GabiBrawl/Nibunkatsu/assets/day2image5.png

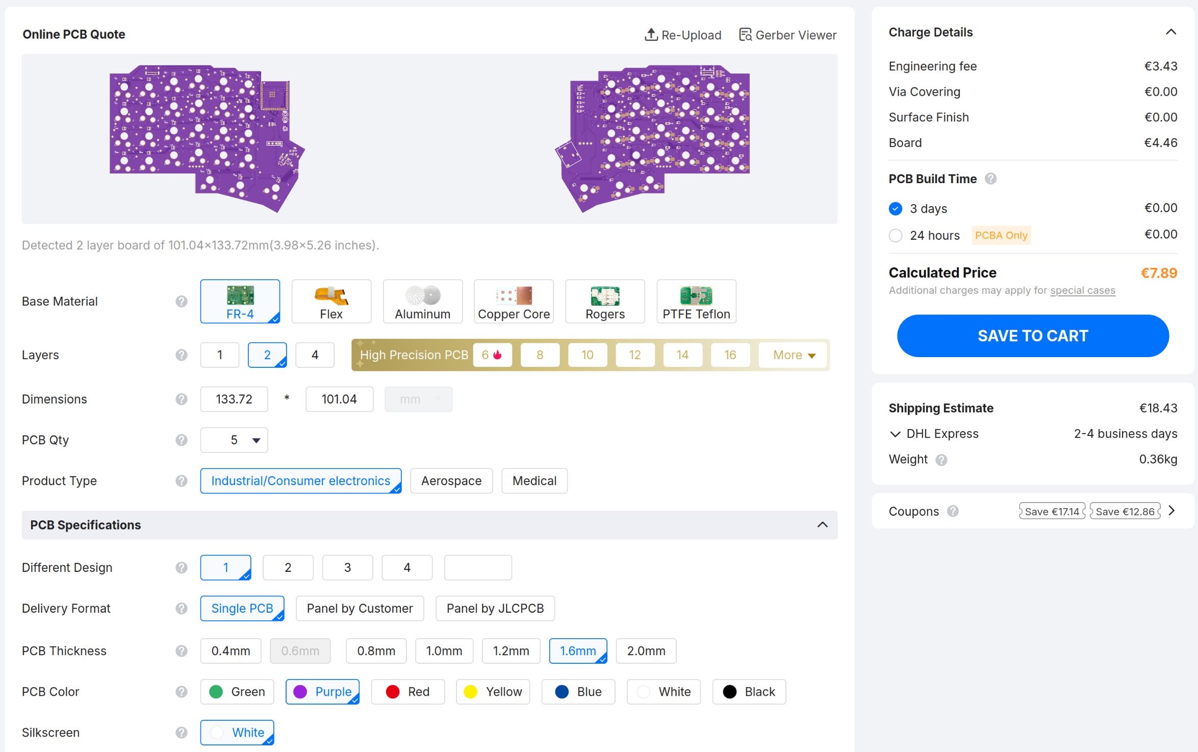
assets/day2image5.png
