GabiBrawl/Nibunkatsu/assets/day5image1.png

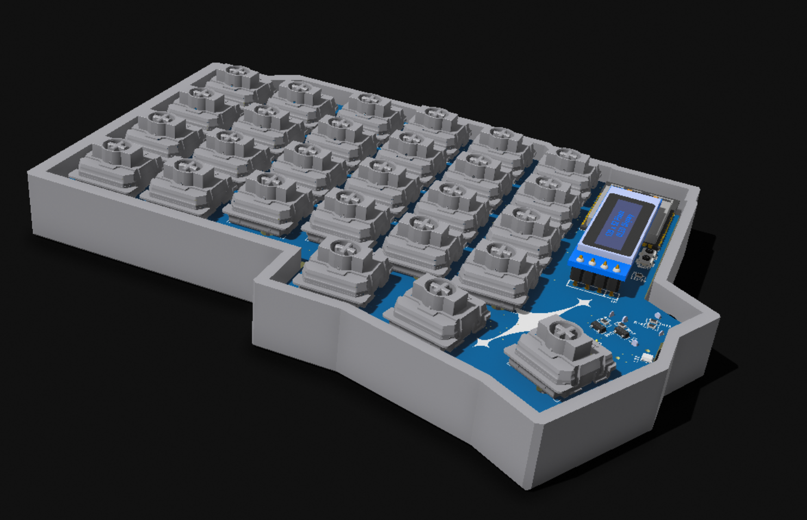
assets/day5image1.png
