GabiBrawl/Nibunkatsu/assets/day5image2.png

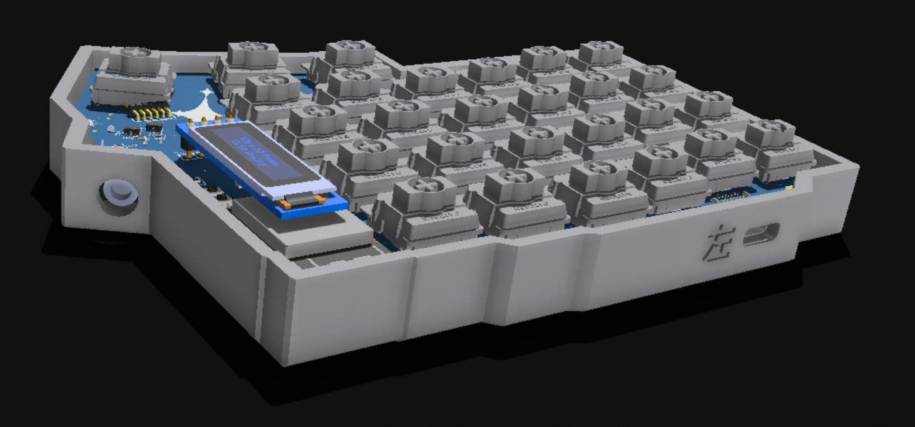
assets/day5image2.png
