GabiBrawl/Nibunkatsu/assets/day5image3.png

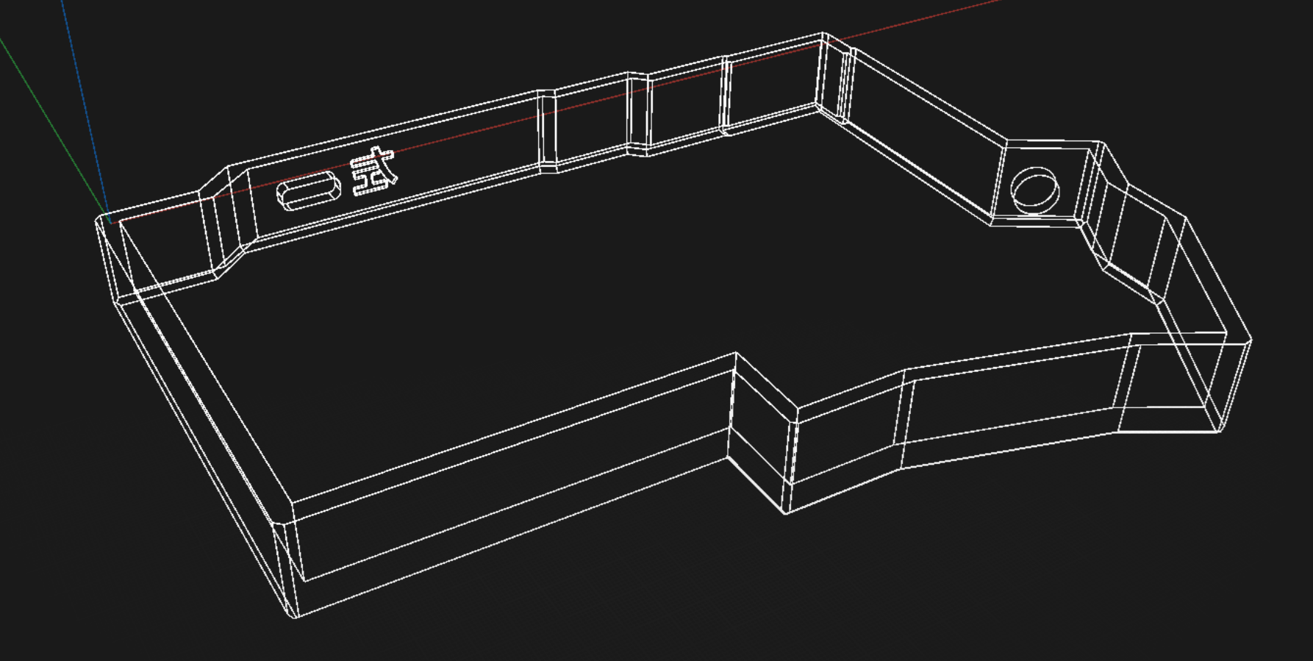
assets/day5image3.png
