GabiBrawl/Nibunkatsu/assets/day5image7.png

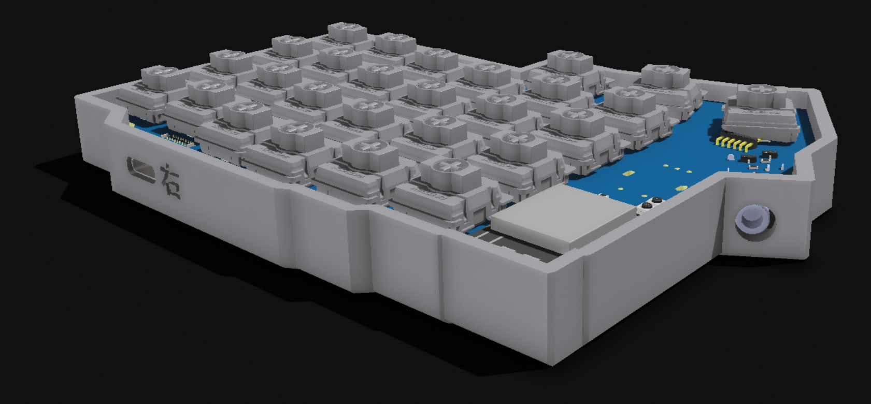
assets/day5image7.png
