GabiBrawl/Nibunkatsu/assets/day5image9.png

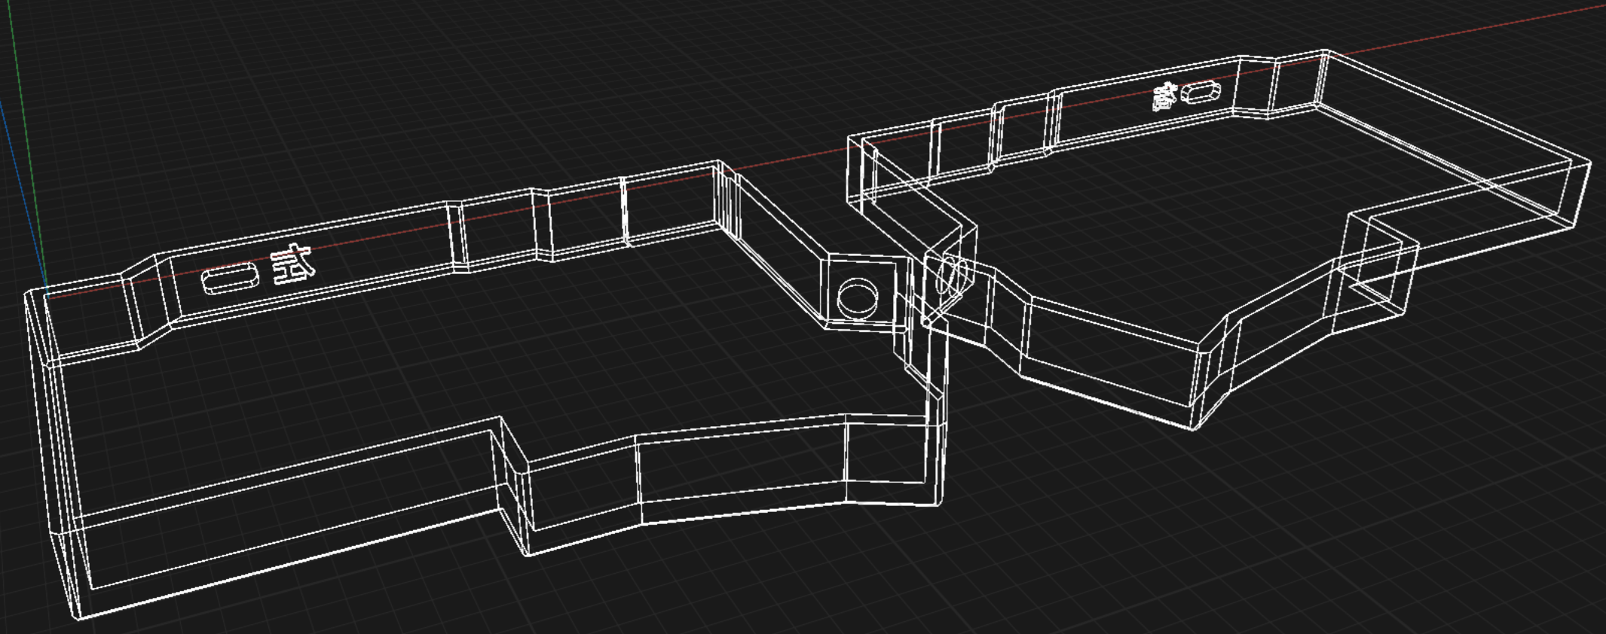
assets/day5image9.png
