GabiBrawl/Nibunkatsu/assets/day6image2.png

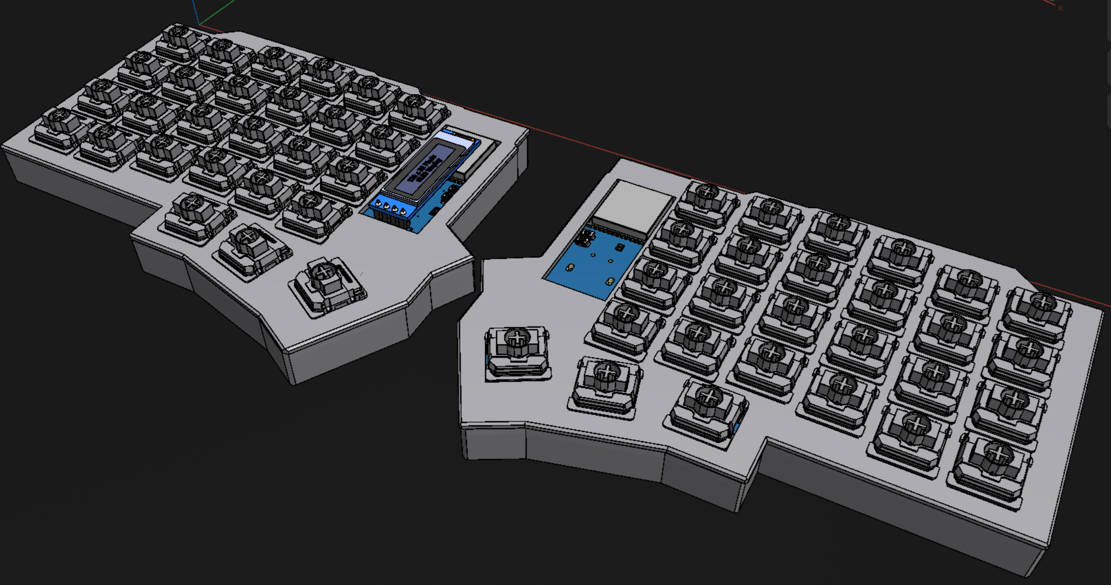
assets/day6image2.png
