GabiBrawl/Nibunkatsu/assets/hero.png

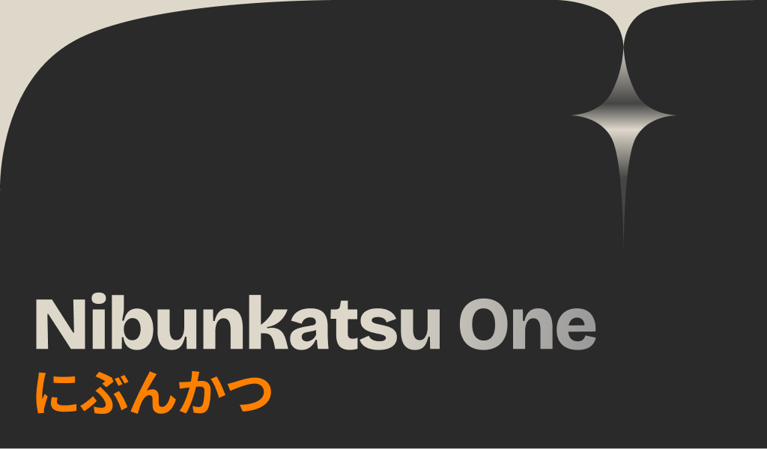
assets/hero.png
