GabiBrawl/Nibunkatsu/firmware/VerticalScreenMockup2.png

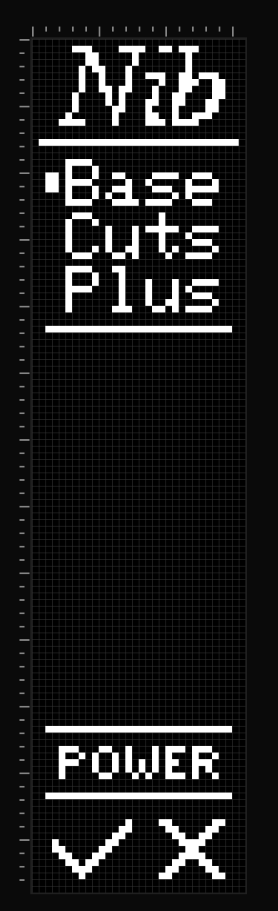
firmware/VerticalScreenMockup2.png
